arianasadeghi/InkTime-Smartwatch/IMAGES/explodedView.png

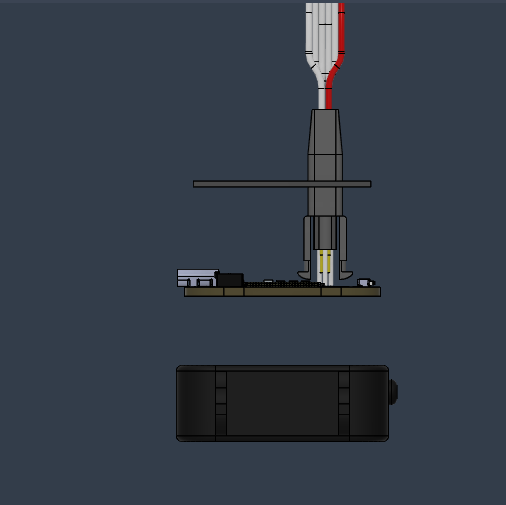
IMAGES/explodedView.png
